physiii/open-dash/daughter/code/main/services/drivers/ads111x/ads111x.h

/**
 * @file ads111x.h
 * @defgroup ads111x ads111x
 * @{
 *
 * ESP-IDF driver for ADS1113/ADS1114/ADS1115, ADS1013/ADS1014/ADS1015 I2C ADC
 *
 * Ported from esp-open-rtos
 *
 * Copyright (C) 2016, 2018 Ruslan V. Uss <unclerus@gmail.com>
 * Copyright (C) 2020 Lucio Tarantino (https://github.com/dianlight)
 *
 * BSD Licensed as described in the file LICENSE
 */
#ifndef __ADS111X_H__
#define __ADS111X_H__

#include <stdbool.h>
#include <esp_err.h>
#include "../i2cdev/i2cdev.h"

#ifdef __cplusplus
extern "C" {
#endif

#define ADS111X_ADDR_GND 0x48 //!< I2C device address with ADDR pin connected to ground
#define ADS111X_ADDR_VCC 0x49 //!< I2C device address with ADDR pin connected to VCC
#define ADS111X_ADDR_SDA 0x4a //!< I2C device address with ADDR pin connected to SDA
#define ADS111X_ADDR_SCL 0x4b //!< I2C device address with ADDR pin connected to SCL

#define ADS111X_MAX_VALUE 0x7fff //!< Maximum ADC value
#define ADS101X_MAX_VALUE 0x7ff

// ADS101X overrides
#define ADS101X_DATA_RATE_128  	ADS111X_DATA_RATE_8
#define ADS101X_DATA_RATE_250  	ADS111X_DATA_RATE_16
#define ADS101X_DATA_RATE_490  	ADS111X_DATA_RATE_32
#define ADS101X_DATA_RATE_920  	ADS111X_DATA_RATE_64
#define ADS101X_DATA_RATE_1600	ADS111X_DATA_RATE_128
#define ADS101X_DATA_RATE_2400	ADS111X_DATA_RATE_250
#define ADS101X_DATA_RATE_3300	ADS111X_DATA_RATE_475

/**
 * Gain amplifier
 */
typedef enum
{
    ADS111X_GAIN_6V144 = 0, //!< +-6.144V
    ADS111X_GAIN_4V096,     //!< +-4.096V
    ADS111X_GAIN_2V048,     //!< +-2.048V (default)
    ADS111X_GAIN_1V024,     //!< +-1.024V
    ADS111X_GAIN_0V512,     //!< +-0.512V
    ADS111X_GAIN_0V256,     //!< +-0.256V
    ADS111X_GAIN_0V256_2,   //!< +-0.256V (same as ADS111X_GAIN_0V256)
    ADS111X_GAIN_0V256_3,   //!< +-0.256V (same as ADS111X_GAIN_0V256)
} ads111x_gain_t;

/**
 * Gain amplifier values
 */
extern const float ads111x_gain_values[];

/**
 * Input multiplexer configuration (ADS1115 only)
 */
typedef enum
{
    ADS111X_MUX_0_1 = 0, //!< positive = AIN0, negative = AIN1 (default)
    ADS111X_MUX_0_3,     //!< positive = AIN0, negative = AIN3
    ADS111X_MUX_1_3,     //!< positive = AIN1, negative = AIN3
    ADS111X_MUX_2_3,     //!< positive = AIN2, negative = AIN3
    ADS111X_MUX_0_GND,   //!< positive = AIN0, negative = GND
    ADS111X_MUX_1_GND,   //!< positive = AIN1, negative = GND
    ADS111X_MUX_2_GND,   //!< positive = AIN2, negative = GND
    ADS111X_MUX_3_GND,   //!< positive = AIN3, negative = GND
} ads111x_mux_t;

/**
 * Data rate
 */
typedef enum
{
    ADS111X_DATA_RATE_8 = 0, //!< 8 samples per second
    ADS111X_DATA_RATE_16,    //!< 16 samples per second
    ADS111X_DATA_RATE_32,    //!< 32 samples per second
    ADS111X_DATA_RATE_64,    //!< 64 samples per second
    ADS111X_DATA_RATE_128,   //!< 128 samples per second (default)
    ADS111X_DATA_RATE_250,   //!< 250 samples per second
    ADS111X_DATA_RATE_475,   //!< 475 samples per second
    ADS111X_DATA_RATE_860    //!< 860 samples per second
} ads111x_data_rate_t;

/**
 * Operational mode
 */
typedef enum
{
    ADS111X_MODE_CONTINUOUS = 0, //!< Continuous conversion mode
    ADS111X_MODE_SINGLE_SHOT    //!< Power-down single-shot mode (default)
} ads111x_mode_t;

/**
 * Comparator mode (ADS1114 and ADS1115 only)
 */
typedef enum
{
    ADS111X_COMP_MODE_NORMAL = 0, //!< Traditional comparator with hysteresis (default)
    ADS111X_COMP_MODE_WINDOW      //!< Window comparator
} ads111x_comp_mode_t;

/**
 * Comparator polarity (ADS1114 and ADS1115 only)
 */
typedef enum
{
    ADS111X_COMP_POLARITY_LOW = 0, //!< Active low (default)
    ADS111X_COMP_POLARITY_HIGH     //!< Active high
} ads111x_comp_polarity_t;

/**
 * Comparator latch (ADS1114 and ADS1115 only)
 */
typedef enum
{
    ADS111X_COMP_LATCH_DISABLED = 0, //!< Non-latching comparator (default)
    ADS111X_COMP_LATCH_ENABLED       //!< Latching comparator
} ads111x_comp_latch_t;

/**
 * Comparator queue
 */
typedef enum
{
    ADS111X_COMP_QUEUE_1 = 0,   //!< Assert ALERT/RDY pin after one conversion
    ADS111X_COMP_QUEUE_2,       //!< Assert ALERT/RDY pin after two conversions
    ADS111X_COMP_QUEUE_4,       //!< Assert ALERT/RDY pin after four conversions
    ADS111X_COMP_QUEUE_DISABLED //!< Disable comparator (default)
} ads111x_comp_queue_t;

/**
 * @brief Initialize device descriptor
 *
 * @param dev Device descriptor
 * @param addr Device address
 * @param port I2C port number
 * @param sda_gpio GPIO pin for SDA
 * @param scl_gpio GPIO pin for SCL
 * @return `ESP_OK` on success
 */
esp_err_t ads111x_init_desc(i2c_dev_t *dev, uint8_t addr, i2c_port_t port,
        gpio_num_t sda_gpio, gpio_num_t scl_gpio);

/**
 * @brief Free device descriptor
 *
 * @param dev Device descriptor
 * @return `ESP_OK` on success
 */
esp_err_t ads111x_free_desc(i2c_dev_t *dev);

/**
 * @brief Get device operational status
 *
 * @param dev Device descriptor
 * @param[out] busy True when device performing conversion
 * @return `ESP_OK` on success
 */
esp_err_t ads111x_is_busy(i2c_dev_t *dev, bool *busy);

/**
 * @brief Begin a single conversion
 *
 * Only in single-shot mode.
 *
 * @param dev Device descriptor
 * @return `ESP_OK` on success
 */
esp_err_t ads111x_start_conversion(i2c_dev_t *dev);

/**
 * @brief Read last conversion result
 *
 * @param dev Device descriptor
 * @param[out] value Last conversion result
 * @return `ESP_OK` on success
 */
esp_err_t ads111x_get_value(i2c_dev_t *dev, int16_t *value);

/**
 * @brief Read last conversion result for ADS101x
 *
 * @param dev Device descriptor
 * @param[out] value Last conversion result
 * @return `ESP_OK` on success
 */
esp_err_t ads101x_get_value(i2c_dev_t *dev, int16_t *value);

/**
 * @brief Read the programmable gain amplifier configuration
 *
 * ADS1114 and ADS1115 only.
 * Use ::ads111x_gain_values[] for real voltage.
 *
 * @param dev Device descriptor
 * @param[out] gain Gain value
 * @return `ESP_OK` on success
 */
esp_err_t ads111x_get_gain(i2c_dev_t *dev, ads111x_gain_t *gain);

/**
 * @brief Configure the programmable gain amplifier
 *
 * ADS1114 and ADS1115 only.
 *
 * @param dev Device descriptor
 * @param gain Gain value
 * @return `ESP_OK` on success
 */
esp_err_t ads111x_set_gain(i2c_dev_t *dev, ads111x_gain_t gain);

/**
 * @brief Read the input multiplexer configuration
 *
 * ADS1115 only.
 *
 * @param dev Device descriptor
 * @param[out] mux Input multiplexer configuration
 * @return `ESP_OK` on success
 */
esp_err_t ads111x_get_input_mux(i2c_dev_t *dev, ads111x_mux_t *mux);

/**
 * @brief Configure the input multiplexer configuration
 *
 * ADS1115 only.
 *
 * @param dev Device descriptor
 * @param mux Input multiplexer configuration
 * @return `ESP_OK` on success
 */
esp_err_t ads111x_set_input_mux(i2c_dev_t *dev, ads111x_mux_t mux);

/**
 * @brief Read the device operating mode
 *
 * @param dev Device descriptor
 * @param[out] mode Device operating mode
 * @return `ESP_OK` on success
 */
esp_err_t ads111x_get_mode(i2c_dev_t *dev, ads111x_mode_t *mode);

/**
 * @brief Set the device operating mode
 *
 * @param dev Device descriptor
 * @param mode Device operating mode
 * @return `ESP_OK` on success
 */
esp_err_t ads111x_set_mode(i2c_dev_t *dev, ads111x_mode_t mode);

/**
 * @brief Read the data rate
 *
 * @param dev Device descriptor
 * @param[out] rate Data rate
 * @return `ESP_OK` on success
 */
esp_err_t ads111x_get_data_rate(i2c_dev_t *dev, ads111x_data_rate_t *rate);

/**
 * @brief Configure the data rate
 *
 * @param dev Device descriptor
 * @param rate Data rate
 * @return `ESP_OK` on success
 */
esp_err_t ads111x_set_data_rate(i2c_dev_t *dev, ads111x_data_rate_t rate);

/**
 * @brief Get comparator mode
 *
 * ADS1114 and ADS1115 only.
 *
 * @param dev Device descriptor
 * @param[out] mode Comparator mode
 * @return `ESP_OK` on success
 */
esp_err_t ads111x_get_comp_mode(i2c_dev_t *dev, ads111x_comp_mode_t *mode);

/**
 * @brief Set comparator mode
 *
 * ADS1114 and ADS1115 only.
 *
 * @param dev Device descriptor
 * @param mode Comparator mode
 * @return `ESP_OK` on success
 */
esp_err_t ads111x_set_comp_mode(i2c_dev_t *dev, ads111x_comp_mode_t mode);

/**
 * @brief Get polarity of the comparator output pin ALERT/RDY
 *
 * ADS1114 and ADS1115 only.
 *
 * @param dev Device descriptor
 * @param[out] polarity Comparator output pin polarity
 * @return `ESP_OK` on success
 */
esp_err_t ads111x_get_comp_polarity(i2c_dev_t *dev, ads111x_comp_polarity_t *polarity);

/**
 * @brief Set polarity of the comparator output pin ALERT/RDY
 *
 * ADS1114 and ADS1115 only.
 *
 * @param dev Device descriptor
 * @param polarity Comparator output pin polarity
 * @return `ESP_OK` on success
 */
esp_err_t ads111x_set_comp_polarity(i2c_dev_t *dev, ads111x_comp_polarity_t polarity);

/**
 * @brief Get comparator output latch mode
 *
 * ADS1114 and ADS1115 only.
 *
 * @param dev Device descriptor
 * @param[out] latch Comparator output latch mode
 * @return `ESP_OK` on success
 */
esp_err_t ads111x_get_comp_latch(i2c_dev_t *dev, ads111x_comp_latch_t *latch);

/**
 * @brief Set comparator output latch mode
 *
 * ADS1114 and ADS1115 only.
 *
 * @param dev Device descriptor
 * @param latch Comparator output latch mode
 * @return `ESP_OK` on success
 */
esp_err_t ads111x_set_comp_latch(i2c_dev_t *dev, ads111x_comp_latch_t latch);

/**
 * @brief Get comparator queue size
 *
 * Get number of the comparator conversions before pin ALERT/RDY
 * assertion. ADS1114 and ADS1115 only.
 *
 * @param dev Device descriptor
 * @param[out] queue Number of the comparator conversions
 * @return `ESP_OK` on success
 */
esp_err_t ads111x_get_comp_queue(i2c_dev_t *dev, ads111x_comp_queue_t *queue);

/**
 * @brief Set comparator queue size
 *
 * Set number of the comparator conversions before pin ALERT/RDY
 * assertion or disable comparator. ADS1114 and ADS1115 only.
 *
 * @param dev Device descriptor
 * @param queue Number of the comparator conversions
 * @return `ESP_OK` on success
 */
esp_err_t ads111x_set_comp_queue(i2c_dev_t *dev, ads111x_comp_queue_t queue);

/**
 * @brief Get the lower threshold value used by comparator
 *
 * @param dev Device descriptor
 * @param[out] th Lower threshold value
 * @return `ESP_OK` on success
 */
esp_err_t ads111x_get_comp_low_thresh(i2c_dev_t *dev, int16_t *th);

/**
 * @brief Set the lower threshold value used by comparator
 *
 * @param dev Device descriptor
 * @param th Lower threshold value
 * @return `ESP_OK` on success
 */
esp_err_t ads111x_set_comp_low_thresh(i2c_dev_t *dev, int16_t th);

/**
 * @brief Get the upper threshold value used by comparator
 *
 * @param dev Device descriptor
 * @param[out] th Upper threshold value
 * @return `ESP_OK` on success
 */
esp_err_t ads111x_get_comp_high_thresh(i2c_dev_t *dev, int16_t *th);

/**
 * @brief Set the upper threshold value used by comparator
 *
 * @param dev Device descriptor
 * @param th Upper threshold value
 * @return `ESP_OK` on success
 */
esp_err_t ads111x_set_comp_high_thresh(i2c_dev_t *dev, int16_t th);

#ifdef __cplusplus
}
#endif

/**@}*/

#endif /* __ADS111X_H__ */
