physiii/open-dash/daughter/code/main/services/drivers/i2c.c

/* i2c - Example

   For other examples please check:
   https://github.com/espressif/esp-idf/tree/master/examples

   See README.md file to get detailed usage of this example.

   This example code is in the Public Domain (or CC0 licensed, at your option.)

   Unless required by applicable law or agreed to in writing, this
   software is distributed on an "AS IS" BASIS, WITHOUT WARRANTIES OR
   CONDITIONS OF ANY KIND, either express or implied.
*/
#include <stdio.h>
#include "esp_log.h"
#include "driver/i2c.h"
#include "sdkconfig.h"

static const char *TAG = "i2c-example";

#define _I2C_NUMBER(num) I2C_NUM_##num
#define I2C_NUMBER(num) _I2C_NUMBER(num)

#define I2C_MASTER_SCL_IO 22               /*!< gpio number for I2C master clock */
#define I2C_MASTER_SDA_IO 21               /*!< gpio number for I2C master data  */
#define I2C_MASTER_NUM I2C_NUMBER(0) /*!< I2C port number for master dev */
#define I2C_MASTER_FREQ_HZ 100000        /*!< I2C master clock frequency */
#define I2C_MASTER_TX_BUF_DISABLE 0                           /*!< I2C master doesn't need buffer */
#define I2C_MASTER_RX_BUF_DISABLE 0                           /*!< I2C master doesn't need buffer */

#define WRITE_BIT I2C_MASTER_WRITE              /*!< I2C master write */
#define READ_BIT I2C_MASTER_READ                /*!< I2C master read */
#define ACK_CHECK_EN 0x1                        /*!< I2C master will check ack from slave*/
#define ACK_CHECK_DIS 0x0                       /*!< I2C master will not check ack from slave */
#define ACK_VAL 0x0                             /*!< I2C ack value */
#define NACK_VAL 0x1                            /*!< I2C nack value */


/**
 * @brief test code to read esp-i2c-slave
 *        We need to fill the buffer of esp slave device, then master can read them out.
 *
 * _______________________________________________________________________________________
 * | start | slave_addr + rd_bit +ack | read n-1 bytes + ack | read 1 byte + nack | stop |
 * --------|--------------------------|----------------------|--------------------|------|
 *
 */
static esp_err_t i2c_master_read_slave(uint8_t ADDR, i2c_port_t i2c_num, uint8_t *data_rd, size_t size)
{
    if (size == 0) {
        return ESP_OK;
    }
    i2c_cmd_handle_t cmd = i2c_cmd_link_create();
    i2c_master_start(cmd);
    i2c_master_write_byte(cmd, (ADDR << 1) | READ_BIT, ACK_CHECK_EN);
    if (size > 1) {
        i2c_master_read(cmd, data_rd, size - 1, ACK_VAL);
    }
    i2c_master_read_byte(cmd, data_rd + size - 1, NACK_VAL);
    i2c_master_stop(cmd);
    esp_err_t ret = i2c_master_cmd_begin(i2c_num, cmd, 1000 / portTICK_RATE_MS);
    i2c_cmd_link_delete(cmd);
    return ret;
}

/**
 * @brief Test code to write esp-i2c-slave
 *        Master device write data to slave(both esp32),
 *        the data will be stored in slave buffer.
 *        We can read them out from slave buffer.
 *
 * ___________________________________________________________________
 * | start | slave_addr + wr_bit + ack | write n bytes + ack  | stop |
 * --------|---------------------------|----------------------|------|
 *
 */
static esp_err_t i2c_master_write_slave(uint8_t ADDR, i2c_port_t i2c_num, uint8_t *data_wr, size_t size)
{
    i2c_cmd_handle_t cmd = i2c_cmd_link_create();
    i2c_master_start(cmd);
    i2c_master_write_byte(cmd, (ADDR << 1) | WRITE_BIT, ACK_CHECK_EN);
    i2c_master_write(cmd, data_wr, size, ACK_CHECK_EN);
    i2c_master_stop(cmd);
    esp_err_t ret = i2c_master_cmd_begin(i2c_num, cmd, 1000 / portTICK_RATE_MS);
    i2c_cmd_link_delete(cmd);
    return ret;
}

/**
 * @brief i2c master initialization
 */
static esp_err_t i2c_master_init(void)
{
    int i2c_master_port = I2C_MASTER_NUM;
    i2c_config_t conf;
    conf.mode = I2C_MODE_MASTER;
    conf.sda_io_num = I2C_MASTER_SDA_IO;
    conf.sda_pullup_en = GPIO_PULLUP_ENABLE;
    conf.scl_io_num = I2C_MASTER_SCL_IO;
    conf.scl_pullup_en = GPIO_PULLUP_ENABLE;
    conf.master.clk_speed = I2C_MASTER_FREQ_HZ;
		conf.clk_flags = 0;
    i2c_param_config(i2c_master_port, &conf);
    return i2c_driver_install(i2c_master_port, conf.mode, I2C_MASTER_RX_BUF_DISABLE, I2C_MASTER_TX_BUF_DISABLE, 0);
}

void i2c_main(void)
{
    ESP_ERROR_CHECK(i2c_master_init());
}
